alessandroCharbonnier/ballisticSolver/src/display.h

#pragma once
/// @file display.h
/// @brief OLED display manager for SH1106 128×64 I2C.

#include <U8g2lib.h>
#include <ballistic.h>
#include "config.h"

// AppState values (avoid circular include with modes.h)
constexpr uint8_t APP_STATE_MENU          = 0;
constexpr uint8_t APP_STATE_LIVE          = 1;
constexpr uint8_t APP_STATE_STAGE         = 2;
constexpr uint8_t APP_STATE_SENSORS       = 3;
constexpr uint8_t APP_STATE_DIGITAL_LEVEL = 4;

/// Display layout (128×64 monochrome, monospace fonts):
///   Y  0–9   : mode header + WiFi icon          (5×8 font)
///   Y 12–23  : distance / target info            (6×12 font)
///   Y 26–39  : vertical correction               (7×14 font)
///   Y 42–55  : horizontal correction             (7×14 font)
///   Y 58–63  : sensor bar                        (5×8 font)

class Display {
public:
    void begin();
    void update();

    // --- State setters ---
    void setAppState(uint8_t state);
    void setMenuCursor(uint8_t cursor);
    void setWifiOn(bool on);
    void setCant(float cant_deg);
    void setCantCalibration(float offset, float sensitivity);
    void showShutdown();
    void clearScreen();
    void showWakeProgress(uint8_t pct);
    void setDimmed(bool dim);

    // --- Data setters (called from main loop) ---
    void setMode(bool staged, uint8_t stage_idx = 0, uint8_t stage_total = 0);
    void setStageName(const char* name);
    void setDistance(uint16_t yards);
    void setCorrection(const ballistic::CorrectionResult& corr,
                       ballistic::CorrectionUnit unit);
    void setSensors(float temp_f, float press_inhg, float humidity_pct);
    void setHeading(float heading_deg);
    void setCompassCalibrating(bool active);
    void setWind(float speed_mph, float angle_deg, bool available);
    void setUnitDistance(uint8_t u);
    void setUnitTemperature(uint8_t u);
    void setUnitPressure(uint8_t u);
    void setWifiActive(bool active);
    void setLiveDigitCursor(uint8_t pos);   // 0=thousands, 1=hundreds, ...
    void setBattery(float pct, float volts);

private:
    U8G2_SH1106_128X64_NONAME_F_HW_I2C u8g2_{U8G2_R0, U8X8_PIN_NONE};

    // State
    bool     staged_       = false;
    uint8_t  stage_idx_    = 0;
    uint8_t  stage_total_  = 0;
    char     stage_name_[17] = {0};
    uint16_t distance_yd_  = 0;
    bool     wifi_active_  = false;
    uint8_t  digit_cursor_ = 1;   // live mode cursor position (0-3)

    // Menu & cant state
    uint8_t  app_state_    = APP_STATE_MENU;
    uint8_t  menu_cursor_  = 0;
    uint8_t  menu_scroll_   = 0; // first visible menu item index
    bool     wifi_menu_on_ = false;
    float    cant_deg_        = 0.0f;
    float    cant_offset_     = 0.0f;
    float    cant_sensitivity_= 1.0f;
    bool     inverted_        = false;
    bool     dimmed_           = false;

    // Correction display
    float    v_corr_       = 0.0f;
    bool     v_up_         = true;
    float    h_corr_       = 0.0f;
    bool     h_right_      = true;
    char     unit_label_[6] = "MOA";

    // Sensors
    float    temp_f_       = 59.0f;
    float    press_inhg_   = 29.92f;
    float    humidity_     = 0.0f;
    float    heading_deg_   = 0.0f;
    float    wind_speed_mph_= 0.0f;
    float    wind_angle_deg_= 0.0f;
    bool     wind_ok_       = false;
    float    battery_pct_   = -1.0f;   // battery 0–100 (−1 = unavailable)
    float    battery_v_      = 0.0f;    // raw battery voltage
    uint8_t  unit_distance_    = 0;
    uint8_t  unit_temperature_ = 0;
    uint8_t  unit_pressure_    = 0;
    bool     compass_cal_     = false;  // compass calibration in progress

    void drawHeader();
    void drawDistance();
    void drawCorrections();
    void drawSensorBar();
    void drawMenu();
    void drawSensorView();
    void drawCantSlider();
    void drawDigitalLevel();
    void drawArrowUp(int x, int y);
    void drawArrowDown(int x, int y);
    void drawArrowRight(int x, int y);
    void drawArrowLeft(int x, int y);
};
