alessandroCharbonnier/ballisticSolver/test/test_compare/main.cpp

/// @file test_compare_output.cpp
/// @brief Outputs trajectory data for comparison with py_ballisticcalc.
///
/// Prints CSV rows for each test scenario/distance pair so the
/// Python comparison script can validate the C++ engine against
/// the reference Python library.
///
/// Output format:
///   scenario,dist_yd,drop_in,windage_in,vel_fps,mach,time_s,energy_ftlb

#include <cstdio>
#include <vector>
#include <ballistic.h>

using namespace ballistic;

struct Scenario {
    const char* name;
    double bc;
    DragTableId table;
    double weight_gr;
    double diameter_in;
    double length_in;
    double mv_fps;
    double sight_height_in;
    double twist_in;
    double zero_yd;
    double temp_f;
    double press_inhg;
    double humidity;
    double wind_fps;
    double wind_dir;      // degrees  (0 = tail, 90 = from left)
    double max_range_yd;
    double step_yd;
};

struct MultiBCScenario {
    const char* name;
    const BCPoint* bc_pts;
    size_t bc_count;
    DragTableId table;
    double weight_gr;
    double diameter_in;
    double length_in;
    double mv_fps;
    double sight_height_in;
    double twist_in;
    double zero_yd;
    double temp_f;
    double press_inhg;
    double humidity;
    double wind_fps;
    double wind_dir;
    double max_range_yd;
    double step_yd;
};

struct PowderSensScenario {
    const char* name;
    double bc;
    DragTableId table;
    double weight_gr;
    double diameter_in;
    double length_in;
    double mv_fps;
    double sight_height_in;
    double twist_in;
    double zero_yd;
    double ref_temp_f;     // baseline powder temperature
    double fps_per_degf;   // raw sensitivity: fps velocity change per °F
    double temp_f;
    double press_inhg;
    double humidity;
    double wind_fps;
    double wind_dir;
    double max_range_yd;
    double step_yd;
};

static void runScenario(const Scenario& s) {
    Calculator calc;
    calc.configure(s.bc, s.table,
                   s.weight_gr, s.diameter_in, s.length_in,
                   s.mv_fps, s.sight_height_in, s.twist_in, s.zero_yd);
    calc.setAtmosphere(s.temp_f, s.press_inhg, s.humidity);
    calc.setWind(s.wind_fps, s.wind_dir);
    if (!calc.solve()) {
        fprintf(stderr, "WARN: zero failed for %s\n", s.name);
    }

    auto traj = calc.trajectory(s.max_range_yd, s.step_yd);
    for (const auto& pt : traj) {
        double dist_yd = pt.distance_ft / kFeetPerYard;
        double drop_in = pt.height_ft * kInchesPerFoot;
        double wind_in = pt.windage_ft * kInchesPerFoot;
        printf("%s,%.1f,%.4f,%.4f,%.2f,%.4f,%.6f,%.2f\n",
               s.name, dist_yd, drop_in, wind_in,
               pt.velocity_fps, pt.mach, pt.time_s, pt.energy_ftlb);
    }
}

static void runMultiBCScenario(const MultiBCScenario& s) {
    Calculator calc;
    calc.configureMultiBC(s.bc_pts, s.bc_count, s.table,
                          s.weight_gr, s.diameter_in, s.length_in,
                          s.mv_fps, s.sight_height_in, s.twist_in, s.zero_yd);
    calc.setAtmosphere(s.temp_f, s.press_inhg, s.humidity);
    calc.setWind(s.wind_fps, s.wind_dir);
    if (!calc.solve()) {
        fprintf(stderr, "WARN: zero failed for %s\n", s.name);
    }

    auto traj = calc.trajectory(s.max_range_yd, s.step_yd);
    for (const auto& pt : traj) {
        double dist_yd = pt.distance_ft / kFeetPerYard;
        double drop_in = pt.height_ft * kInchesPerFoot;
        double wind_in = pt.windage_ft * kInchesPerFoot;
        printf("%s,%.1f,%.4f,%.4f,%.2f,%.4f,%.6f,%.2f\n",
               s.name, dist_yd, drop_in, wind_in,
               pt.velocity_fps, pt.mach, pt.time_s, pt.energy_ftlb);
    }
}

static void runPowderSensScenario(const PowderSensScenario& s) {
    Calculator calc;
    calc.configure(s.bc, s.table,
                   s.weight_gr, s.diameter_in, s.length_in,
                   s.mv_fps, s.sight_height_in, s.twist_in, s.zero_yd);
    // Derive normalized modifier from raw fps/°F sensitivity
    double modifier = s.fps_per_degf * 15.0 / s.mv_fps;
    calc.setPowderSensitivity(s.ref_temp_f, modifier);
    calc.setAtmosphere(s.temp_f, s.press_inhg, s.humidity);
    calc.setWind(s.wind_fps, s.wind_dir);
    if (!calc.solve()) {
        fprintf(stderr, "WARN: zero failed for %s\n", s.name);
    }

    auto traj = calc.trajectory(s.max_range_yd, s.step_yd);
    for (const auto& pt : traj) {
        double dist_yd = pt.distance_ft / kFeetPerYard;
        double drop_in = pt.height_ft * kInchesPerFoot;
        double wind_in = pt.windage_ft * kInchesPerFoot;
        printf("%s,%.1f,%.4f,%.4f,%.2f,%.4f,%.6f,%.2f\n",
               s.name, dist_yd, drop_in, wind_in,
               pt.velocity_fps, pt.mach, pt.time_s, pt.energy_ftlb);
    }
}

int main() {
    printf("scenario,dist_yd,drop_in,windage_in,vel_fps,mach,time_s,energy_ftlb\n");

    // ════════════════════════════════════════════════════════════════════
    // ORIGINAL BASELINE SCENARIOS
    // ════════════════════════════════════════════════════════════════════

    // ── 6.5 Creedmoor G7, std atmo, no wind ────────────────────────────
    runScenario({
        "65cm_g7_std",
        0.315, DragTableId::G7,
        140.0, 0.264, 1.35,
        2710.0, 1.5, 8.0, 100.0,
        59.0, 29.92, 0.0,
        0.0, 0.0,
        2000.0, 100.0
    });

    // ── .308 Winchester G7, std atmo, 10 mph crosswind ──────────────────
    runScenario({
        "308_g7_wind",
        0.243, DragTableId::G7,
        175.0, 0.308, 1.24,
        2600.0, 1.5, 10.0, 100.0,
        59.0, 29.92, 0.0,
        14.667, 90.0,
        1500.0, 100.0
    });

    // ── .338 Lapua G7, hot weather ──────────────────────────────────────
    runScenario({
        "338lm_g7_hot",
        0.417, DragTableId::G7,
        300.0, 0.338, 1.70,
        2750.0, 1.5, 9.375, 100.0,
        100.0, 29.50, 0.50,
        0.0, 0.0,
        2500.0, 100.0
    });

    // ── .50 BMG G1, std atmo ────────────────────────────────────────────
    runScenario({
        "50bmg_g1_std",
        1.050, DragTableId::G1,
        750.0, 0.510, 2.31,
        2820.0, 2.0, 15.0, 100.0,
        59.0, 29.92, 0.0,
        0.0, 0.0,
        2500.0, 100.0
    });

    // ── 6mm Creedmoor G7, cold weather ──────────────────────────────────
    runScenario({
        "6cm_g7_cold",
        0.275, DragTableId::G7,
        105.0, 0.243, 1.30,
        3050.0, 1.5, 7.5, 100.0,
        20.0, 30.10, 0.20,
        0.0, 0.0,
        1500.0, 100.0
    });

    // ── .300 PRC G7 at altitude ─────────────────────────────────────────
    runScenario({
        "300prc_g7_alt",
        0.391, DragTableId::G7,
        230.0, 0.308, 1.60,
        2800.0, 1.5, 8.0, 100.0,
        70.0, 24.90, 0.30,
        0.0, 0.0,
        2000.0, 100.0
    });

    // ── .308 Winchester G1 ──────────────────────────────────────────────
    runScenario({
        "308_g1_std",
        0.462, DragTableId::G1,
        175.0, 0.308, 1.24,
        2600.0, 1.5, 10.0, 100.0,
        59.0, 29.92, 0.0,
        0.0, 0.0,
        1500.0, 100.0
    });

    // ── .375 CheyTac G7, extreme long range ─────────────────────────────
    runScenario({
        "375ct_g7_elr",
        0.465, DragTableId::G7,
        350.0, 0.375, 2.00,
        2750.0, 1.5, 10.0, 100.0,
        59.0, 29.92, 0.0,
        0.0, 0.0,
        3000.0, 100.0
    });

    // ════════════════════════════════════════════════════════════════════
    // .22 LR — COMPETITION BULLET BRANDS (King of 22LR distances)
    // All: dia=0.223", twist=16", zero=50yd, step=25yd, max=300yd
    // ════════════════════════════════════════════════════════════════════

    // SK Rifle Match — popular mid-tier match, 40gr LRN
    runScenario({
        "22lr_sk_rifle_std",
        0.131, DragTableId::RA4,
        40.0, 0.223, 0.43,
        1073.0, 1.5, 16.0, 50.0,
        59.0, 29.92, 0.0,
        0.0, 0.0,
        300.0, 25.0
    });

    // SK Long Range Match — optimized for distance, 40gr
    runScenario({
        "22lr_sk_lr_std",
        0.140, DragTableId::RA4,
        40.0, 0.223, 0.43,
        1082.0, 1.5, 16.0, 50.0,
        59.0, 29.92, 0.0,
        0.0, 0.0,
        300.0, 25.0
    });

    // Eley Tenex — gold standard .22 LR match ammo, 40gr flat-nose
    runScenario({
        "22lr_tenex_std",
        0.145, DragTableId::RA4,
        40.0, 0.223, 0.43,
        1085.0, 1.5, 16.0, 50.0,
        59.0, 29.92, 0.0,
        0.0, 0.0,
        300.0, 25.0
    });

    // Eley ELR (Contact) — subsonic design for long-range .22 LR, 42gr
    runScenario({
        "22lr_eley_elr_std",
        0.162, DragTableId::RA4,
        42.0, 0.223, 0.47,
        1040.0, 1.5, 16.0, 50.0,
        59.0, 29.92, 0.0,
        0.0, 0.0,
        300.0, 25.0
    });

    // Lapua Center-X — consistent precision, 40gr
    runScenario({
        "22lr_centerx_std",
        0.138, DragTableId::RA4,
        40.0, 0.223, 0.43,
        1073.0, 1.5, 16.0, 50.0,
        59.0, 29.92, 0.0,
        0.0, 0.0,
        300.0, 25.0
    });

    // Lapua Midas+ — top-tier Lapua match, 40gr
    runScenario({
        "22lr_midas_std",
        0.143, DragTableId::RA4,
        40.0, 0.223, 0.43,
        1090.0, 1.5, 16.0, 50.0,
        59.0, 29.92, 0.0,
        0.0, 0.0,
        300.0, 25.0
    });

    // Lapua Long Range — designed for 50-100m competition, 40gr
    runScenario({
        "22lr_lap_lr_std",
        0.141, DragTableId::RA4,
        40.0, 0.223, 0.43,
        1073.0, 1.5, 16.0, 50.0,
        59.0, 29.92, 0.0,
        0.0, 0.0,
        300.0, 25.0
    });

    // Lapua Super Long Range — designed for 100m+ competition, 40gr
    runScenario({
        "22lr_lap_slr_std",
        0.147, DragTableId::RA4,
        40.0, 0.223, 0.43,
        1066.0, 1.5, 16.0, 50.0,
        59.0, 29.92, 0.0,
        0.0, 0.0,
        300.0, 25.0
    });

    // Lapua X-Act — ultimate precision, 40gr
    runScenario({
        "22lr_xact_std",
        0.145, DragTableId::RA4,
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

    // 10 mph headwind
    runScenario({
        "65cm_147_headwind",
        0.351, DragTableId::G7,
        147.0, 0.264, 1.42,
        2695.0, 1.5, 8.0, 100.0,
        59.0, 29.92, 0.0,
        14.667, 180.0,
        1200.0, 50.0
    });

    // 10 mph tailwind
    runScenario({
        "65cm_147_tailwind",
        0.351, DragTableId::G7,
        147.0, 0.264, 1.42,
        2695.0, 1.5, 8.0, 100.0,
        59.0, 29.92, 0.0,
        14.667, 0.0,
        1200.0, 50.0
    });

    // 10 mph quartering from 45°
    runScenario({
        "65cm_147_qw45",
        0.351, DragTableId::G7,
        147.0, 0.264, 1.42,
        2695.0, 1.5, 8.0, 100.0,
        59.0, 29.92, 0.0,
        14.667, 45.0,
        1200.0, 50.0
    });

    // 10 mph quartering from 135°
    runScenario({
        "65cm_147_qw135",
        0.351, DragTableId::G7,
        147.0, 0.264, 1.42,
        2695.0, 1.5, 8.0, 100.0,
        59.0, 29.92, 0.0,
        14.667, 135.0,
        1200.0, 50.0
    });

    // 20 mph gust full crosswind
    runScenario({
        "65cm_147_gust20",
        0.351, DragTableId::G7,
        147.0, 0.264, 1.42,
        2695.0, 1.5, 8.0, 100.0,
        59.0, 29.92, 0.0,
        29.33, 90.0,
        1200.0, 50.0
    });

    // ════════════════════════════════════════════════════════════════════
    // MULTI-BC SCENARIOS — velocity-stepped ballistic coefficients
    // ════════════════════════════════════════════════════════════════════

    // 6.5 CM Berger 140gr Hybrid Target — 3 velocity-stepped BCs (G7)
    {
        BCPoint pts[] = {{0.315, 2700.0}, {0.310, 2200.0}, {0.290, 1800.0}};
        runMultiBCScenario({
            "mbc_65cm_b140", pts, 3, DragTableId::G7,
            140.0, 0.264, 1.35, 2710.0, 1.5, 8.0, 100.0,
            59.0, 29.92, 0.0, 0.0, 0.0, 1200.0, 50.0
        });
    }

    // 6.5 CM Hornady 147 ELD-M — multi-BC with PRS crosswind
    {
        BCPoint pts[] = {{0.351, 2700.0}, {0.345, 2200.0}, {0.330, 1800.0}};
        runMultiBCScenario({
            "mbc_65cm_147_w10", pts, 3, DragTableId::G7,
            147.0, 0.264, 1.42, 2695.0, 1.5, 8.0, 100.0,
            59.0, 29.92, 0.0, 14.667, 90.0, 1200.0, 50.0
        });
    }

    // .338 LM Berger 300gr Hybrid OTM — 3 BC points (G7)
    {
        BCPoint pts[] = {{0.419, 2750.0}, {0.410, 2200.0}, {0.395, 1700.0}};
        runMultiBCScenario({
            "mbc_338lm_b300", pts, 3, DragTableId::G7,
            300.0, 0.338, 1.70, 2750.0, 1.5, 9.375, 100.0,
            59.0, 29.92, 0.0, 0.0, 0.0, 1760.0, 100.0
        });
    }

    // .300 PRC Berger 230gr Hybrid Target — multi-BC at altitude (G7)
    {
        BCPoint pts[] = {{0.368, 2800.0}, {0.360, 2300.0}, {0.340, 1800.0}};
        runMultiBCScenario({
            "mbc_300prc_b230", pts, 3, DragTableId::G7,
            230.0, 0.308, 1.60, 2825.0, 1.5, 8.0, 100.0,
            70.0, 24.90, 0.30, 0.0, 0.0, 1760.0, 100.0
        });
    }

    // 6mm CM Hornady 110gr A-Tip — multi-BC (G7)
    {
        BCPoint pts[] = {{0.301, 3000.0}, {0.295, 2500.0}, {0.280, 2000.0}};
        runMultiBCScenario({
            "mbc_6cm_atip110", pts, 3, DragTableId::G7,
            110.0, 0.243, 1.38, 3020.0, 1.5, 7.5, 100.0,
            59.0, 29.92, 0.0, 0.0, 0.0, 1200.0, 50.0
        });
    }

    // .308 Win Berger 185gr Juggernaut — multi-BC with wind (G7)
    {
        BCPoint pts[] = {{0.283, 2600.0}, {0.275, 2100.0}, {0.260, 1600.0}};
        runMultiBCScenario({
            "mbc_308_b185_w10", pts, 3, DragTableId::G7,
            185.0, 0.308, 1.32, 2570.0, 1.5, 10.0, 100.0,
            59.0, 29.92, 0.0, 14.667, 90.0, 1200.0, 50.0
        });
    }

    // ════════════════════════════════════════════════════════════════════
    // POWDER SENSITIVITY SCENARIOS — MV adjusted for temperature
    // ════════════════════════════════════════════════════════════════════

    // 6.5 CM 140 ELD-M — cold day (20°F), ref 59°F, ~1.5 fps/°F
    runPowderSensScenario({
        "ps_65cm_140_cold",
        0.315, DragTableId::G7,
        140.0, 0.264, 1.35, 2710.0, 1.5, 8.0, 100.0,
        59.0, 1.5,
        20.0, 30.10, 0.20, 0.0, 0.0, 1200.0, 50.0
    });

    // 6.5 CM 140 ELD-M — hot day (110°F), same sensitivity
    runPowderSensScenario({
        "ps_65cm_140_hot",
        0.315, DragTableId::G7,
        140.0, 0.264, 1.35, 2710.0, 1.5, 8.0, 100.0,
        59.0, 1.5,
        110.0, 29.80, 0.10, 0.0, 0.0, 1200.0, 50.0
    });

    // .308 Win 175 SMK — extreme cold (0°F), ~1.0 fps/°F
    runPowderSensScenario({
        "ps_308_175_cold",
        0.243, DragTableId::G7,
        175.0, 0.308, 1.24, 2600.0, 1.5, 10.0, 100.0,
        59.0, 1.0,
        0.0, 30.50, 0.10, 0.0, 0.0, 1200.0, 50.0
    });

    // .338 LM 300gr — hot desert (115°F), ~1.8 fps/°F
    runPowderSensScenario({
        "ps_338lm_300_hot",
        0.417, DragTableId::G7,
        300.0, 0.338, 1.70, 2750.0, 1.5, 9.375, 100.0,
        59.0, 1.8,
        115.0, 29.70, 0.10, 0.0, 0.0, 1760.0, 100.0
    });

    // 6.5 CM 147 ELD-M — cold (15°F) with crosswind, ~1.5 fps/°F
    runPowderSensScenario({
        "ps_65cm_147_cold_w10",
        0.351, DragTableId::G7,
        147.0, 0.264, 1.42, 2695.0, 1.5, 8.0, 100.0,
        59.0, 1.5,
        15.0, 30.30, 0.15, 14.667, 90.0, 1200.0, 50.0
    });

    // .300 PRC 230gr — cold high-altitude match (25°F, ~5000ft), ~1.2 fps/°F
    runPowderSensScenario({
        "ps_300prc_230_cold_alt",
        0.391, DragTableId::G7,
        230.0, 0.308, 1.60, 2800.0, 1.5, 8.0, 100.0,
        59.0, 1.2,
        25.0, 24.90, 0.20, 0.0, 0.0, 1760.0, 100.0
    });

    return 0;
}
